theycallmeboxy/bassik/models/plate/ortho-225200.dxf

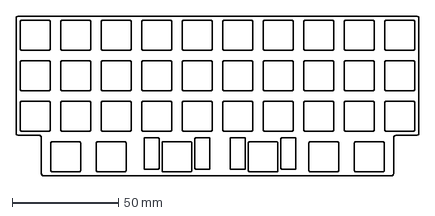
[picture p18: CAD file, 2024-10-12]
models/plate/ortho-225200.dxf
189.4 x 75.2 mm
