theycallmeboxy/bassik/models/plate/ortho-universal.dxf

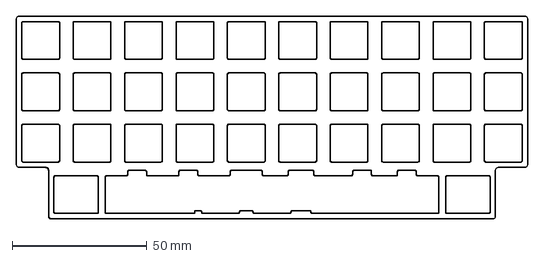
[picture p19: CAD file, 2024-10-12]
models/plate/ortho-universal.dxf
189.4 x 75.2 mm
