theycallmeboxy/bassik/models/plate/ortho-625.dxf

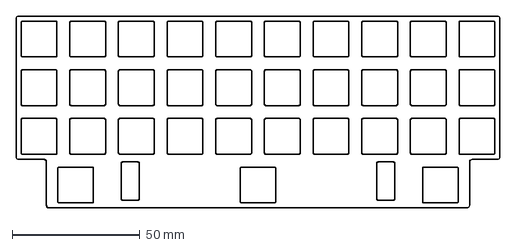
[picture p20: CAD file, 2024-10-12]
models/plate/ortho-625.dxf
189.4 x 75.2 mm
