theycallmeboxy/bassik/models/plate/uni-275.dxf

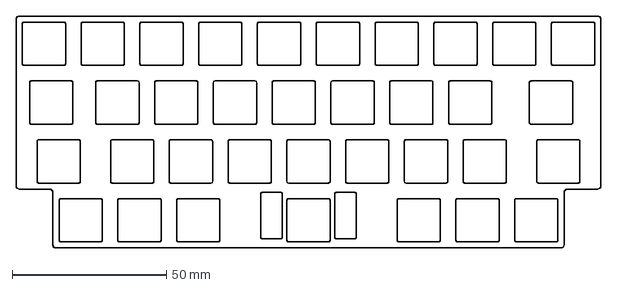
[picture p21: CAD file, 2024-10-12]
models/plate/uni-275.dxf
189.4 x 75.2 mm
