theycallmeboxy/bassik/pcb/bassik v1/bassik.kicad_sch

## KiCad design pcb/bassik v1/bassik.kicad_sch (2024-10-12)

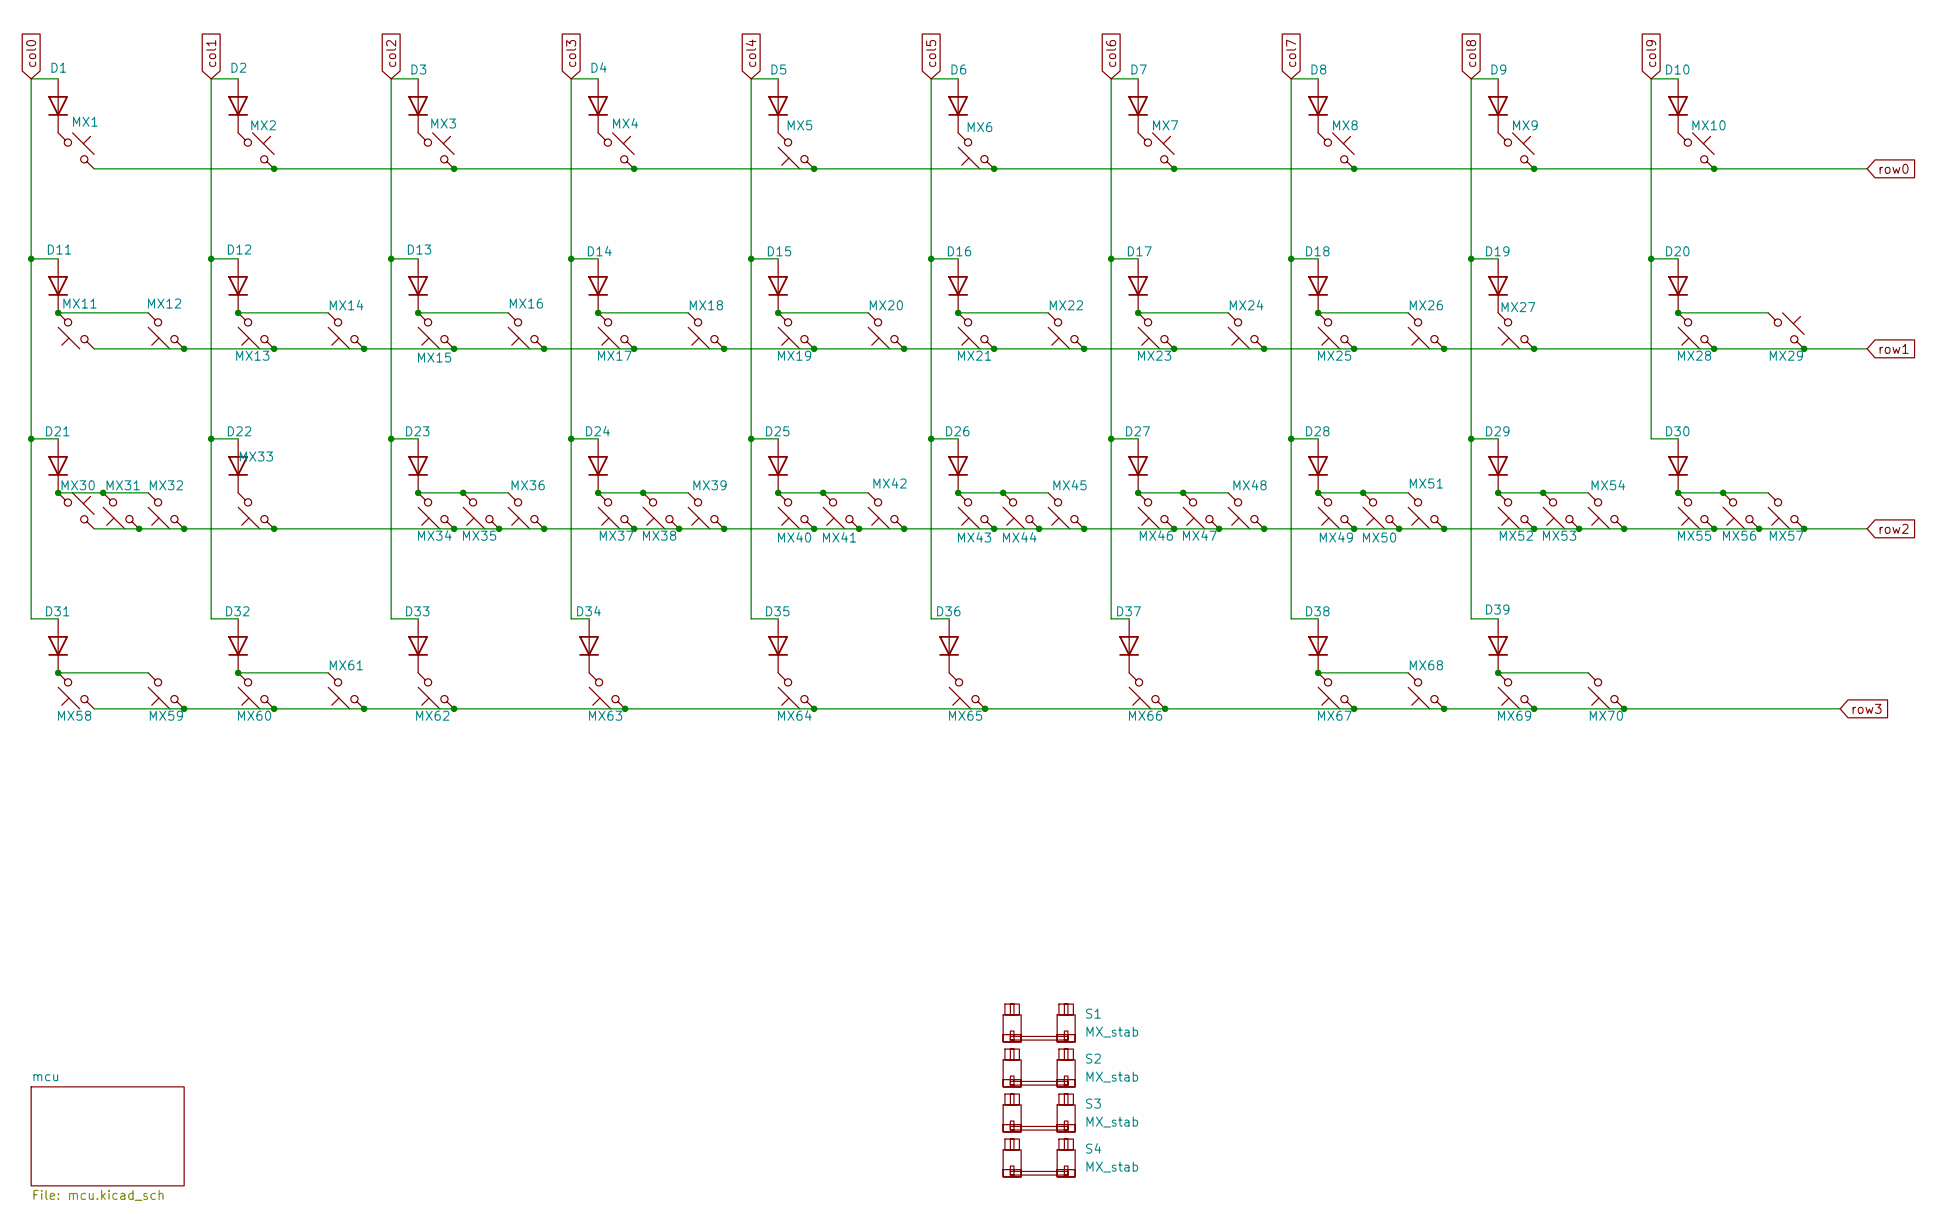
[picture p22: schematic bassik.kicad_sch]

Parts:
D1, D2, D3, D4, D5, D6, D7, D8, D9, D10, D11, D12, D13, D14, D15, D16, D17, D18, D19, D20, D21, D22, D23, D24, D25, D26, D27, D28, D29, D30, D31, D32, D33, D34, D35, D36, D37, D38, D39: D; D_SOD-123
MX1, MX2, MX3, MX4, MX5, MX6, MX7, MX8, MX9, MX10, MX11, MX13, MX14, MX15, MX16, MX17, MX18, MX19, MX20, MX21, MX22, MX23, MX24, MX25, MX26, MX27, MX29, MX30, MX33, MX34, MX35, MX36, MX37, MX38, MX39, MX40, MX41, MX42, MX43, MX44, MX45, MX46, MX47, MX48, MX49, MX50, MX51, MX52, MX53, MX54, MX57, MX58, MX60, MX61, MX62, MX63, MX64, MX65, MX66, MX67, MX68, MX70: MX_SW_solder; SW_MX_1u
MX12, MX56, MX59, MX69: MX_SW_solder; SW_MX_1.25u
MX28, MX32: MX_SW_solder; SW_MX_1.75u
MX31, MX55: MX_SW_solder; SW_MX_1.5u
S1: MX_stab; STAB_MX_6.25u
S2: MX_stab; STAB_MX_2.75u
S3: MX_stab; STAB_MX_2u
S4: MX_stab; STAB_MX_2.25u

Connections:
unnamed: D1.1 (K), MX1.1
unnamed: D2.1 (K), MX2.1
unnamed: D3.1 (K), MX3.1
unnamed: D4.1 (K), MX4.1
unnamed: D5.1 (K), MX5.2
unnamed: D6.1 (K), MX6.2
unnamed: D7.1 (K), MX7.1
unnamed: D8.1 (K), MX8.1
unnamed: D9.1 (K), MX9.1
unnamed: D10.1 (K), MX10.1
unnamed: D11.1 (K), MX11.2, MX12.2
unnamed: D12.1 (K), MX13.2, MX14.2
unnamed: D13.1 (K), MX15.2, MX16.2
unnamed: D14.1 (K), MX17.2, MX18.2
unnamed: D15.1 (K), MX19.2, MX20.2
unnamed: D16.1 (K), MX21.2, MX22.2
unnamed: D17.1 (K), MX23.2, MX24.2
unnamed: D18.1 (K), MX25.2, MX26.2
unnamed: D19.1 (K), MX27.2
unnamed: D20.1 (K), MX28.2, MX29.1
unnamed: D21.1 (K), MX30.1, MX31.2, MX32.2
unnamed: D22.1 (K), MX33.2
unnamed: D23.1 (K), MX34.2, MX35.2, MX36.2
unnamed: D24.1 (K), MX37.2, MX38.2, MX39.2
unnamed: D25.1 (K), MX40.2, MX41.2, MX42.2
unnamed: D26.1 (K), MX43.2, MX44.2, MX45.2
unnamed: D27.1 (K), MX46.2, MX47.2, MX48.2
unnamed: D28.1 (K), MX49.2, MX50.2, MX51.2
unnamed: D29.1 (K), MX52.2, MX53.2, MX54.2
unnamed: D30.1 (K), MX55.2, MX56.2, MX57.2
unnamed: D31.1 (K), MX58.2, MX59.2
unnamed: D32.1 (K), MX60.2, MX61.2
unnamed: D33.1 (K), MX62.2
unnamed: D34.1 (K), MX63.2
unnamed: D35.1 (K), MX64.2
unnamed: D36.1 (K), MX65.2
unnamed: D37.1 (K), MX66.2
unnamed: D38.1 (K), MX67.2, MX68.2
unnamed: D39.1 (K), MX69.2, MX70.2
col0: D1.2 (A), D11.2 (A), D21.2 (A), D31.2 (A)
col1: D2.2 (A), D12.2 (A), D22.2 (A), D32.2 (A)
col2: D3.2 (A), D13.2 (A), D23.2 (A), D33.2 (A)
col3: D4.2 (A), D14.2 (A), D24.2 (A), D34.2 (A)
col4: D5.2 (A), D15.2 (A), D25.2 (A), D35.2 (A)
col5: D6.2 (A), D16.2 (A), D26.2 (A), D36.2 (A)
col6: D7.2 (A), D17.2 (A), D27.2 (A), D37.2 (A)
col7: D8.2 (A), D18.2 (A), D28.2 (A), D38.2 (A)
col8: D9.2 (A), D19.2 (A), D29.2 (A), D39.2 (A)
col9: D10.2 (A), D20.2 (A), D30.2 (A)
row0: MX1.2, MX2.2, MX3.2, MX4.2, MX5.1, MX6.1, MX7.2, MX8.2, MX9.2, MX10.2
row1: MX11.1, MX12.1, MX13.1, MX14.1, MX15.1, MX16.1, MX17.1, MX18.1, MX19.1, MX20.1, MX21.1, MX22.1, MX23.1, MX24.1, MX25.1, MX26.1, MX27.1, MX28.1, MX29.2
row2: MX30.2, MX31.1, MX32.1, MX33.1, MX34.1, MX35.1, MX36.1, MX37.1, MX38.1, MX39.1, MX40.1, MX41.1, MX42.1, MX43.1, MX44.1, MX45.1, MX46.1, MX47.1, MX48.1, MX49.1, MX50.1, MX51.1, MX52.1, MX53.1, MX54.1, MX55.1, MX56.1, MX57.1
row3: MX58.1, MX59.1, MX60.1, MX61.1, MX62.1, MX63.1, MX64.1, MX65.1, MX66.1, MX67.1, MX68.1, MX69.1, MX70.1
